sparkfun/SparkFun_Indoor_Air_Quality_Sensor-SCD41-SEN55/docs/assets/img/Indoor-Air-Quality-Sensor-SEN55_1.jpg

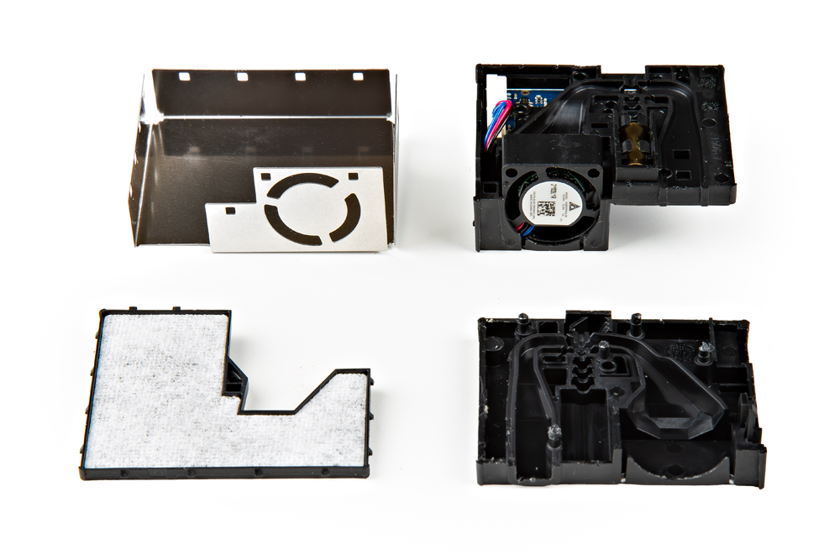
docs/assets/img/Indoor-Air-Quality-Sensor-SEN55_1.jpg
